sparkjl/BB8-Robot/structure/舵机/活动臂1.SLDPRT

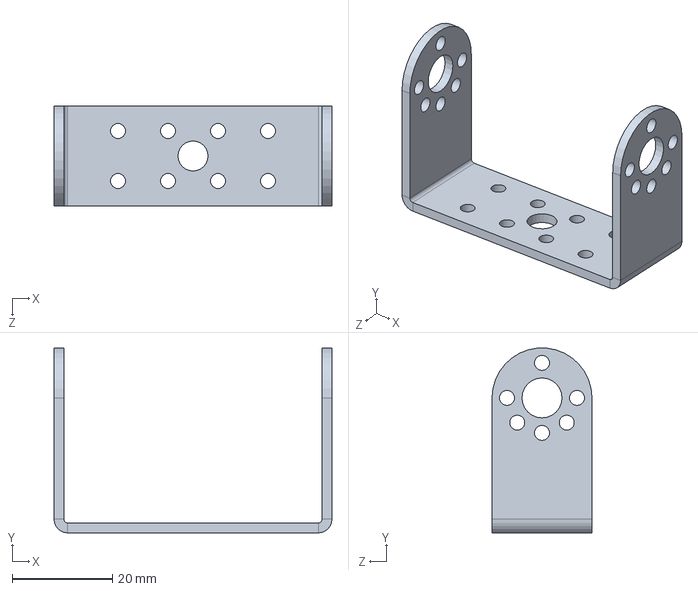
[picture p19: CAD file, 2020-03-29]
structure/舵机/活动臂1.SLDPRT
55.6 x 37.0 x 20.0 mm
