sparkjl/BB8-Robot/structure/万向球.SLDPRT

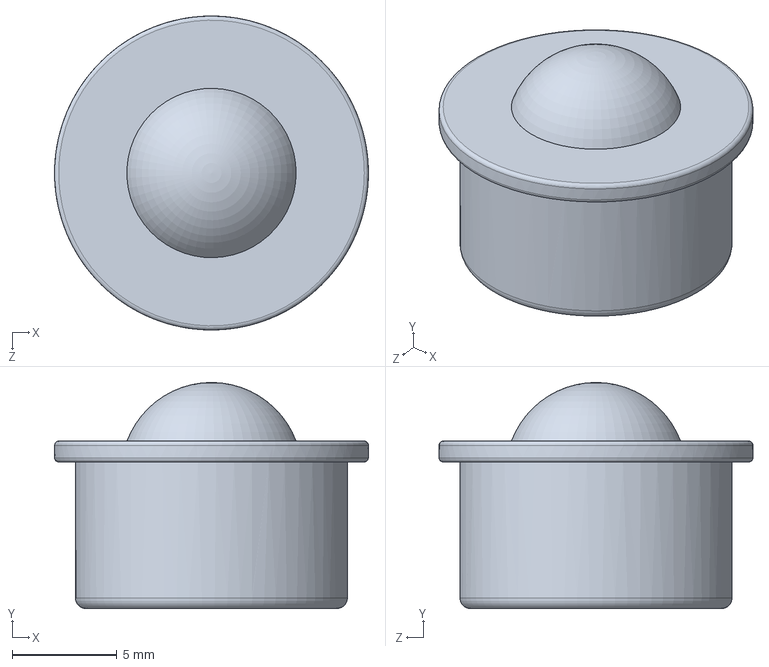
[picture p20: CAD file, 2020-03-29]
structure/万向球.SLDPRT
15.0 x 10.8 x 15.0 mm
