sparkjl/BB8-Robot/structure/外壳/waike3.sldprt

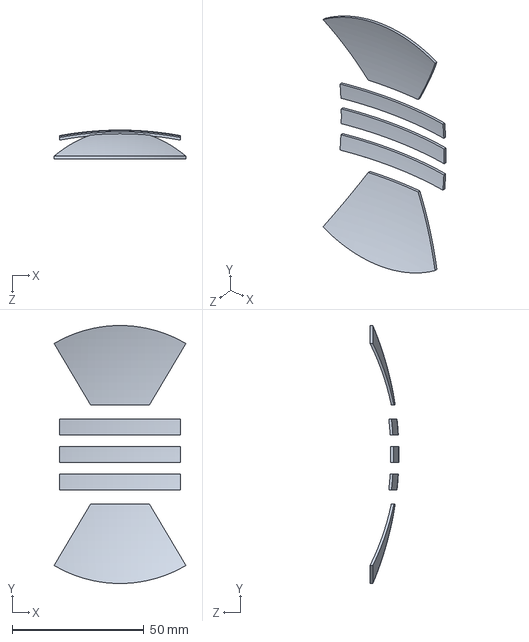
[picture p21: CAD file, 2020-03-29]
structure/外壳/waike3.sldprt
50.1 x 98.0 x 11.0 mm
