sparkjl/BB8-Robot/structure/舵机/活动臂2.SLDPRT

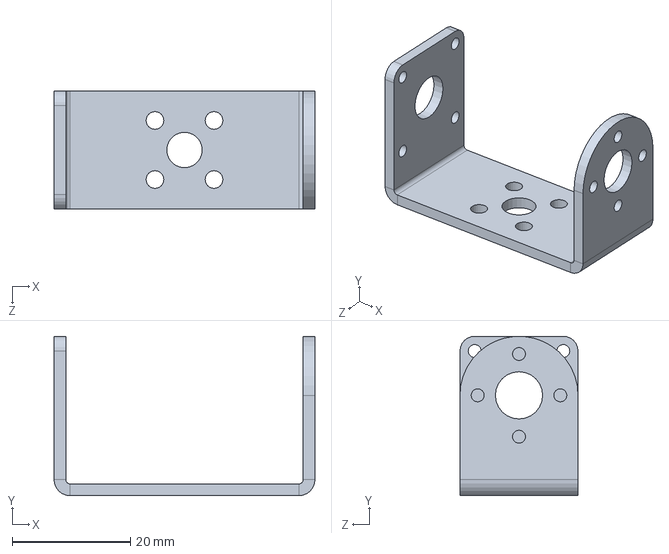
[picture p22: CAD file, 2020-03-29]
structure/舵机/活动臂2.SLDPRT
44.2 x 27.0 x 20.0 mm
