sparkjl/BB8-Robot/structure/外壳/waike1.sldprt

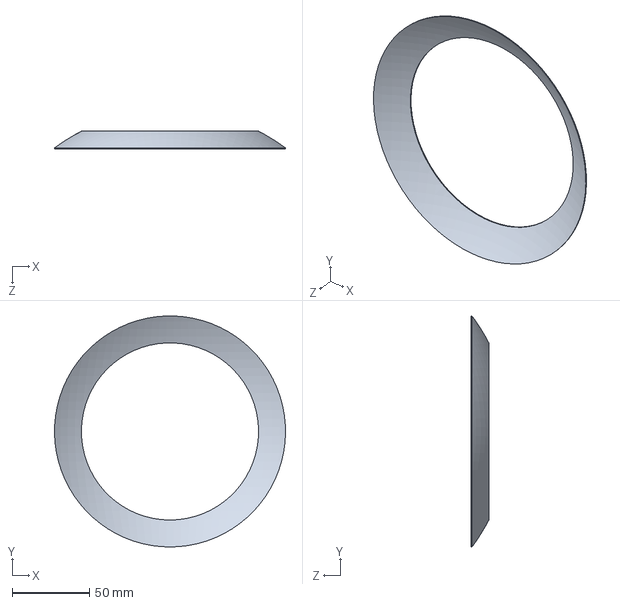
[picture p23: CAD file, 2020-03-29]
structure/外壳/waike1.sldprt
150.0 x 149.9 x 11.5 mm
