sparkjl/BB8-Robot/structure/底盘2.sldprt

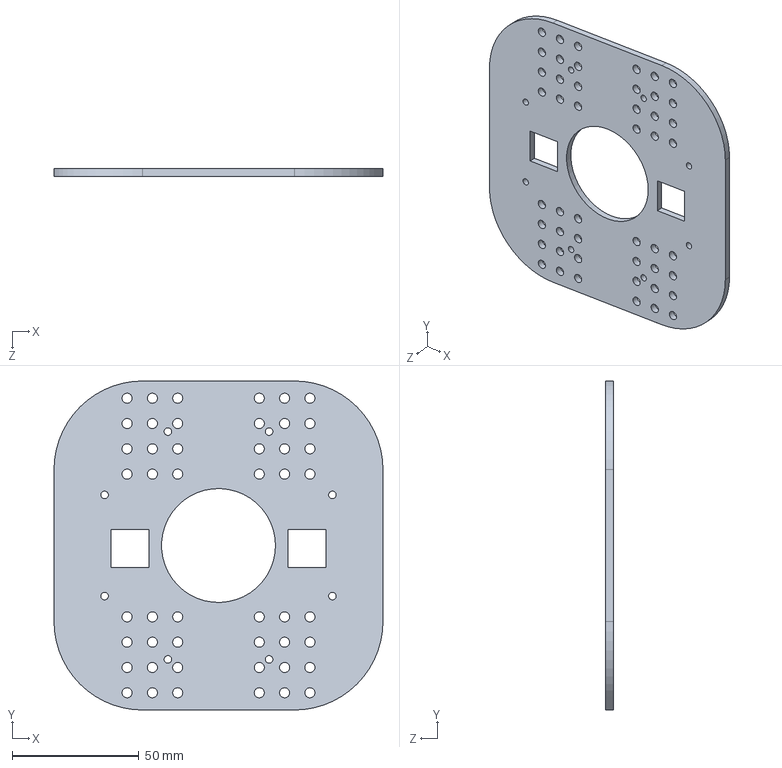
[picture p24: CAD file, 2020-03-29]
structure/底盘2.sldprt
130.0 x 130.0 x 3.00 mm
