sparkjl/BB8-Robot/structure/舵机/舵盘2.SLDPRT

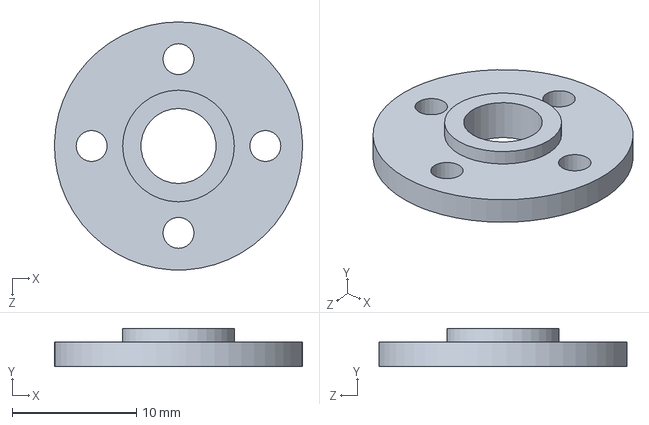
[picture p25: CAD file, 2020-03-29]
structure/舵机/舵盘2.SLDPRT
20.0 x 3.10 x 20.0 mm
