sparkjl/BB8-Robot/structure/外壳/waike4.sldprt

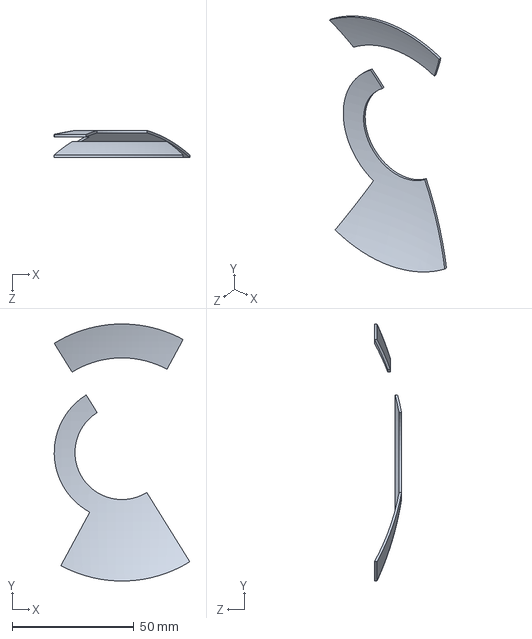
[picture p26: CAD file, 2020-03-29]
structure/外壳/waike4.sldprt
55.6 x 105.4 x 11.1 mm
