sparkjl/BB8-Robot/structure/外壳1.sldprt

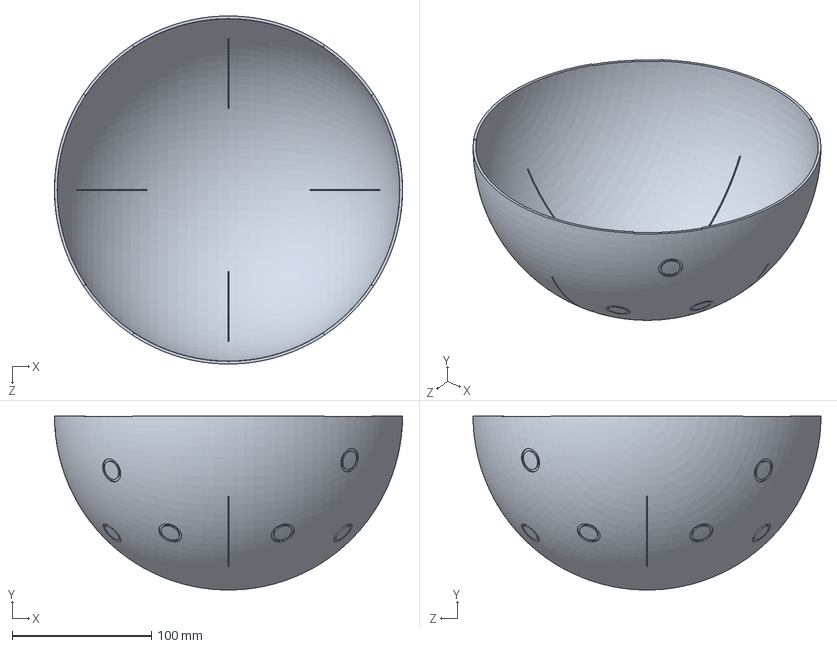
[picture p27: CAD file, 2020-03-29]
structure/外壳1.sldprt
250.0 x 124.9 x 249.9 mm
