sparkjl/BB8-Robot/structure/探头.SLDPRT

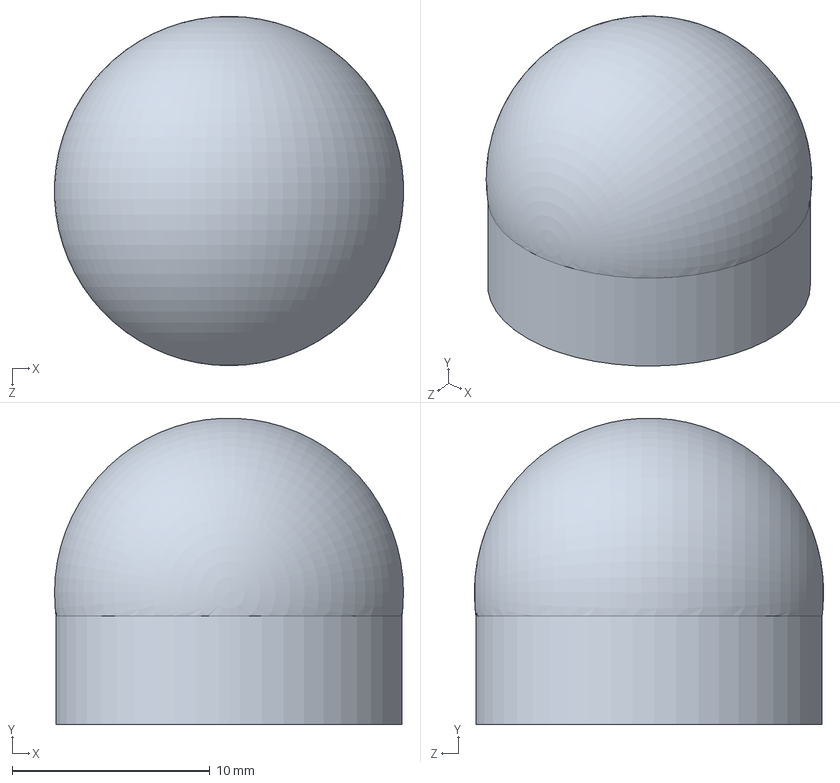
[picture p28: CAD file, 2020-03-29]
structure/探头.SLDPRT
17.6 x 15.5 x 17.7 mm
