sparkjl/BB8-Robot/structure/脖子.sldprt

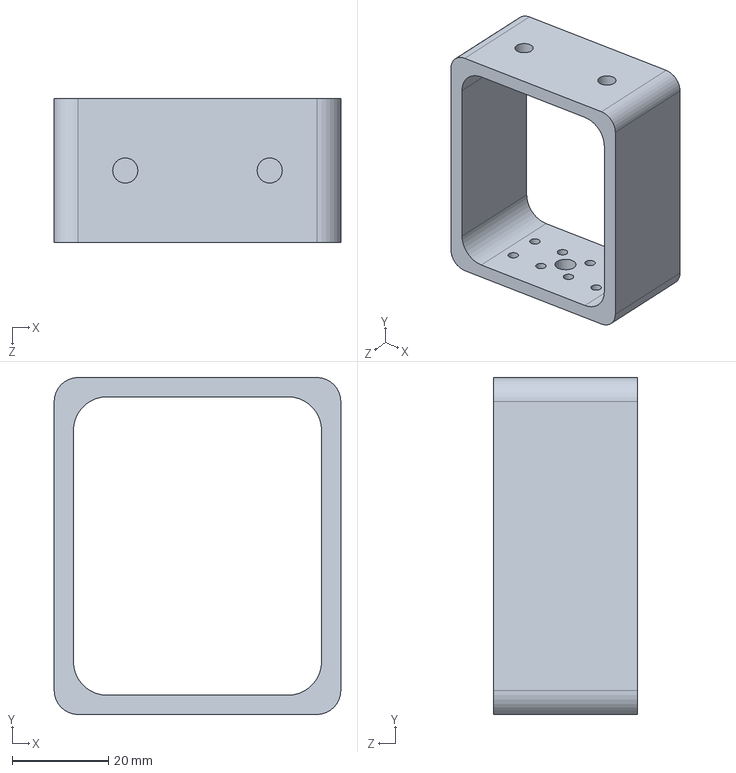
[picture p29: CAD file, 2020-03-29]
structure/脖子.sldprt
59.5 x 70.0 x 30.0 mm
