sparkjl/BB8-Robot/structure/眼睛.SLDPRT

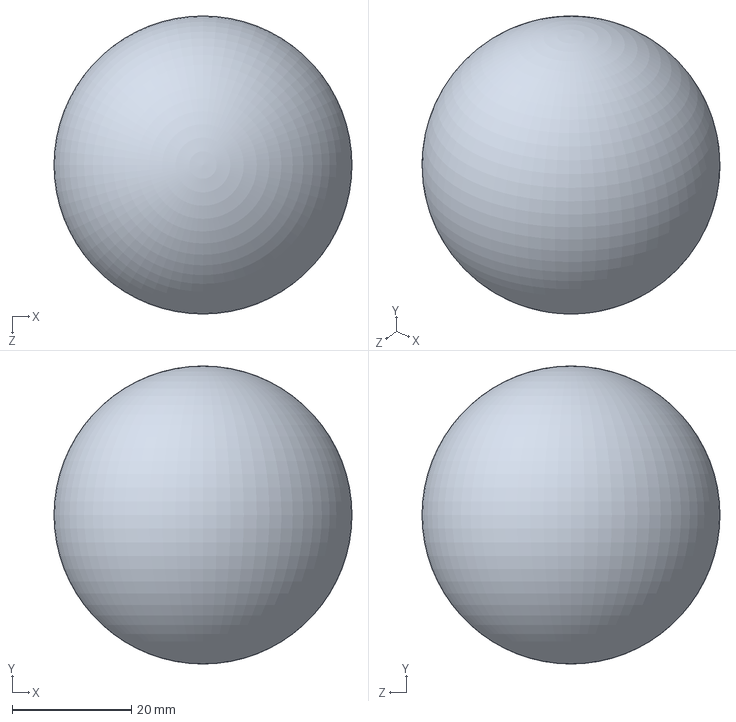
[picture p30: CAD file, 2020-03-29]
structure/眼睛.SLDPRT
50.0 x 50.0 x 50.0 mm
