sparkjl/BB8-Robot/structure/头部.SLDPRT

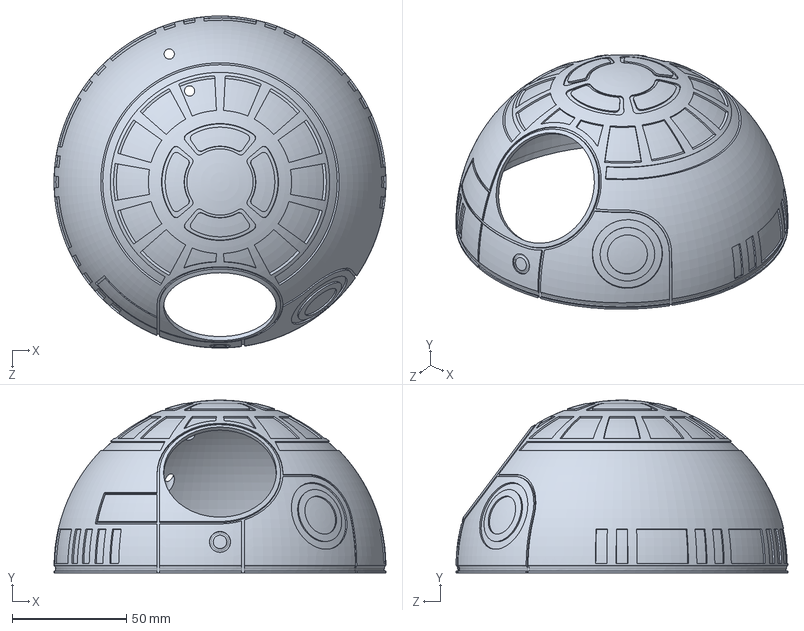
[picture p31: CAD file, 2020-03-29]
structure/头部.SLDPRT
145.0 x 75.5 x 145.0 mm
