sparkjl/BB8-Robot/structure/电池.SLDPRT

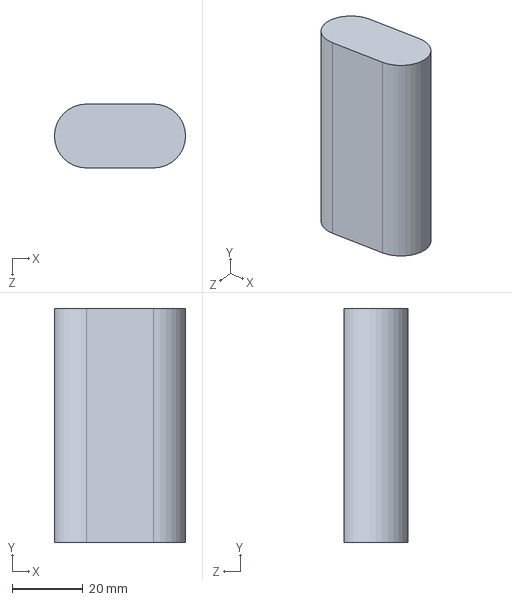
[picture p32: CAD file, 2020-03-29]
structure/电池.SLDPRT
37.0 x 66.0 x 18.0 mm
