sparkjl/BB8-Robot/structure/减速电机.SLDPRT

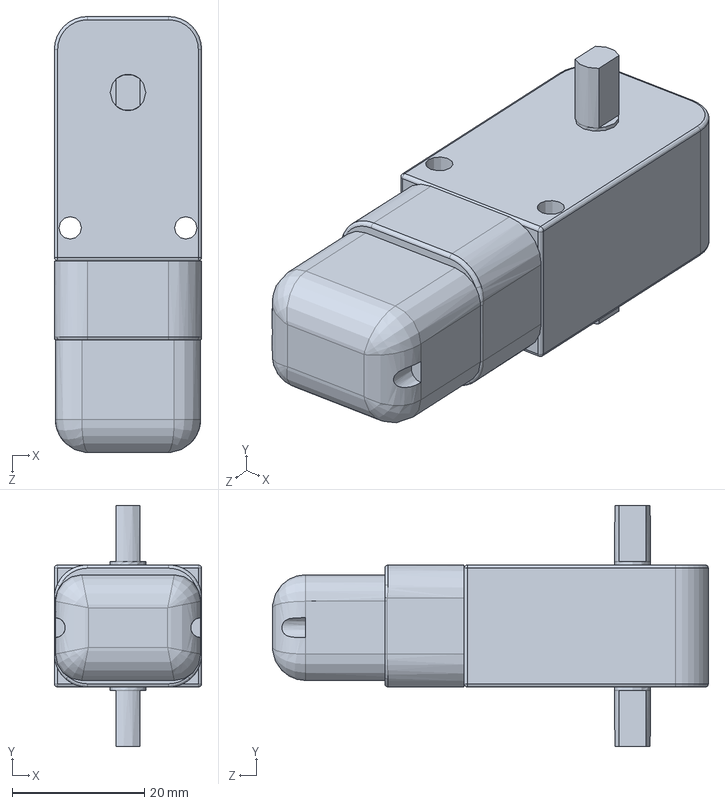
[picture p33: CAD file, 2020-03-29]
structure/减速电机.SLDPRT
22.3 x 36.5 x 66.0 mm
