sparkjl/BB8-Robot/structure/六角双通铜柱M4.sldprt

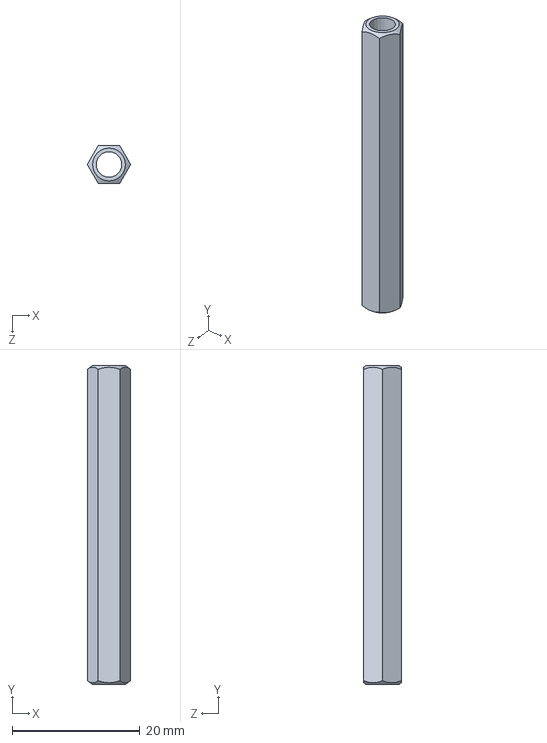
[picture p34: CAD file, 2020-03-29]
structure/六角双通铜柱M4.sldprt
6.81 x 50.0 x 5.90 mm
