sparkjl/BB8-Robot/structure/顶盘.sldprt

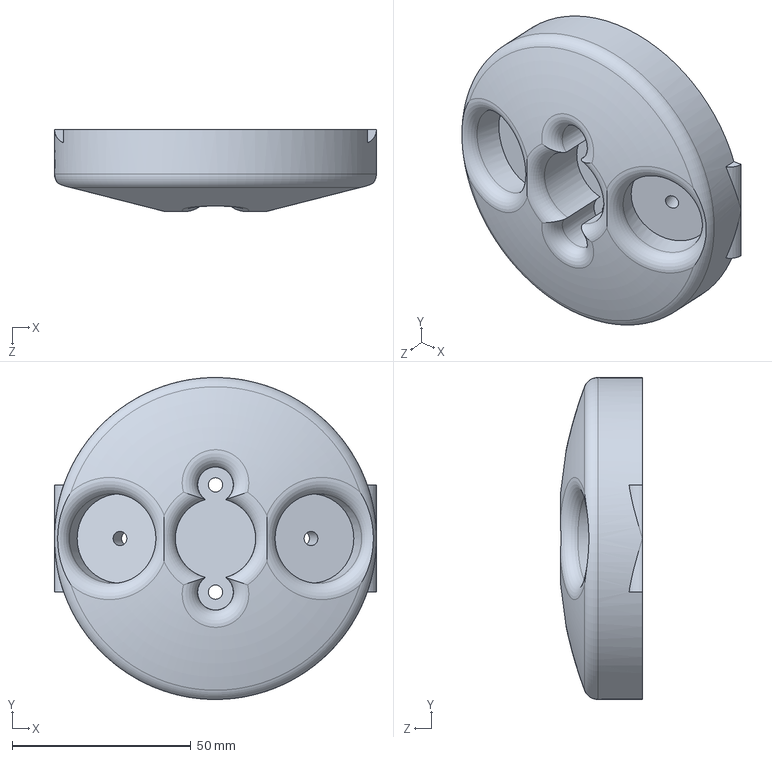
[picture p35: CAD file, 2020-03-29]
structure/顶盘.sldprt
90.0 x 90.0 x 22.9 mm
