sparkjl/BB8-Robot/structure/磁铁.SLDPRT

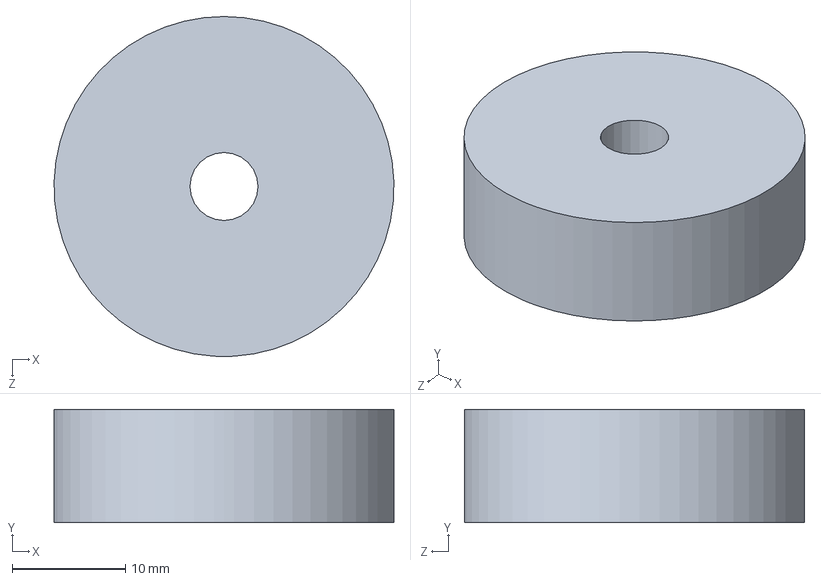
[picture p36: CAD file, 2020-03-29]
structure/磁铁.SLDPRT
30.0 x 10.0 x 30.0 mm
